Shahabaz-Bagwan/ultra-choc-wings/case/ultra_choc_wings_case.scad

// Ultra Choc Wings uniboard case. Generated by scripts/make_case.py from the PCB;
// edit the parameters below, not the data.
//
// One piece holds both halves (left PCB switch side up, right PCB flipped)
// at a fixed splay. Each half drops into its pocket and sits flat on the
// floor (every SMD part is on the top side, so the bottom is bare), held by
// three M2 screws that self-tap into the floor. The CR2032 is reachable from
// the top; the top-edge notch clears the XIAO USB-C and the power switch.

/* [Layout] */
splay = 12;        // degrees each half is rotated away from straight
gap = 18;          // mm between the two halves at their closest point
/* [Walls] */
wall = 2.4;        // side wall thickness
floor_t = 3;       // floor under the PCB
clearance = 0.4;   // gap between PCB edge and pocket wall
pcb_t = 1.6;
lip = 1.0;         // wall height above the PCB top surface
/* [Screws] */
pilot_d = 1.7;     // M2 self-tapping pilot (use 3.2 for M2 heat-set inserts)
pilot_depth = 2.6;
/* [Details] */
xiao_relief_depth = 2;
notch_depth = 10;  // how far the top-edge notch reaches into the wall
center_tray = true; // hollow the deck between the halves
$fn = 48;

board = [[35.195, 62.881], [35.383, 62.824], [35.556, 62.731], [35.707, 62.607], [35.831, 62.456], [35.924, 62.283], [35.981, 62.095], [36.0, 61.9], [36.0, 61.5], [36.019, 61.305], [36.076, 61.117], [36.169, 60.944], [36.293, 60.793], [36.444, 60.669], [36.617, 60.576], [36.805, 60.519], [37.0, 60.5], [44.5, 60.5], [44.695, 60.481], [44.883, 60.424], [45.056, 60.331], [45.207, 60.207], [45.331, 60.056], [45.424, 59.883], [45.481, 59.695], [45.5, 59.5], [45.5, 54.875], [45.519, 54.68], [45.576, 54.492], [45.669, 54.319], [45.793, 54.168], [45.944, 54.044], [46.117, 53.951], [46.305, 53.894], [46.5, 53.875], [62.5, 53.875], [62.695, 53.856], [62.883, 53.799], [63.056, 53.706], [63.207, 53.582], [63.331, 53.431], [63.424, 53.258], [63.481, 53.07], [63.5, 52.875], [63.5, 52.5], [63.519, 52.305], [63.576, 52.117], [63.669, 51.944], [63.793, 51.793], [63.944, 51.669], [64.117, 51.576], [64.305, 51.519], [64.5, 51.5], [80.5, 51.5], [80.695, 51.481], [80.883, 51.424], [81.056, 51.331], [81.207, 51.207], [81.331, 51.056], [81.424, 50.883], [81.481, 50.695], [81.5, 50.5], [81.5, 0.5], [81.273, 0.5], [81.08, 0.481], [80.895, 0.426], [80.724, 0.336], [80.574, 0.215], [80.449, 0.068], [80.356, -0.101], [80.296, -0.285], [80.273, -0.477], [80.287, -0.67], [80.338, -0.856], [80.424, -1.029], [82.174, -3.838], [82.301, -4.0], [82.457, -4.134], [82.638, -4.232], [82.835, -4.291], [83.04, -4.309], [83.244, -4.284], [83.439, -4.218], [83.616, -4.114], [83.769, -3.976], [83.889, -3.809], [84.273, -3.145], [84.387, -2.985], [84.53, -2.851], [84.697, -2.748], [84.88, -2.679], [85.073, -2.647], [85.269, -2.653], [85.46, -2.698], [85.639, -2.779], [100.361, -11.279], [100.521, -11.393], [100.655, -11.536], [100.758, -11.703], [100.827, -11.886], [100.859, -12.079], [100.853, -12.275], [100.808, -12.466], [100.727, -12.645], [93.227, -25.635], [93.113, -25.795], [92.97, -25.929], [92.803, -26.032], [92.62, -26.101], [92.427, -26.133], [92.231, -26.127], [92.04, -26.082], [91.861, -26.001], [79.743, -19.005], [79.57, -18.926], [79.384, -18.881], [79.194, -18.872], [79.005, -18.9], [78.825, -18.963], [75.488, -20.5], [75.385, -20.883], [75.316, -21.067], [75.213, -21.233], [75.079, -21.376], [74.919, -21.49], [74.741, -21.571], [74.55, -21.616], [74.354, -21.622], [74.16, -21.59], [73.852, -21.508], [73.624, -21.474], [73.394, -21.494], [73.175, -21.565], [64.569, -25.53], [64.367, -25.598], [64.155, -25.622], [63.944, -25.601], [33.851, -19.252], [33.641, -19.23], [33.431, -19.253], [33.231, -19.32], [33.049, -19.427], [32.893, -19.57], [32.372, -20.133], [31.822, -20.667], [31.244, -21.171], [30.641, -21.644], [30.013, -22.085], [29.363, -22.492], [28.692, -22.863], [28.003, -23.199], [27.296, -23.498], [26.575, -23.759], [25.841, -23.982], [25.097, -24.165], [24.344, -24.309], [23.584, -24.413], [22.819, -24.477], [22.053, -24.5], [21.286, -24.482], [20.522, -24.424], [19.761, -24.326], [19.007, -24.188], [18.261, -24.01], [17.525, -23.792], [16.802, -23.536], [16.094, -23.243], [15.402, -22.912], [14.729, -22.545], [14.076, -22.143], [13.445, -21.707], [12.838, -21.238], [12.256, -20.738], [11.702, -20.208], [11.177, -19.649], [10.682, -19.064], [10.218, -18.453], [9.788, -17.818], [9.392, -17.161], [9.031, -16.485], [8.706, -15.79], [8.419, -15.079], [8.169, -14.354], [8.085, -14.16], [7.962, -13.989], [7.805, -13.847], [7.623, -13.741], [7.422, -13.676], [-7.933, -10.436], [-8.128, -10.373], [-8.307, -10.272], [-8.46, -10.137], [-8.583, -9.973], [-8.671, -9.788], [-8.718, -9.589], [-8.724, -9.384], [-8.688, -9.182], [-8.612, -8.992], [-8.499, -8.822], [-8.353, -8.678], [-8.131, -8.5], [-8.5, -8.5], [-8.695, -8.481], [-8.883, -8.424], [-9.056, -8.331], [-9.207, -8.207], [-9.331, -8.056], [-9.424, -7.883], [-9.481, -7.695], [-9.5, -7.5], [-9.5, 61.9], [-9.481, 62.095], [-9.424, 62.283], [-9.331, 62.456], [-9.207, 62.607], [-9.056, 62.731], [-8.883, 62.824], [-8.695, 62.881], [-8.5, 62.9], [35.0, 62.9]];
holes = [[2.0, -10.8], [24.5, 59.5], [76.5, -2.5]];
xiao_relief = [-9.14, 42.75, 8.95, 64.41]; // [x0, y0, x1, y1]
notch_x = [-10.14, 22.0];
board_top = 62.9;
coin = [22.0, -10.0];

// Place the left half so its inner edge sits gap/2 left of x = 0.
function rot(p, a) = [p[0] * cos(a) - p[1] * sin(a), p[0] * sin(a) + p[1] * cos(a)];
inner_x = max([for (p = board) rot(p, -splay)[0]]);

module place_left() translate([-gap / 2 - inner_x, 0]) rotate(-splay) children();
module place_right() mirror([1, 0]) place_left() children();
module both() { place_left() children(); place_right() children(); }

h = floor_t + pcb_t + lip;

module board_shape() polygon(board);

module outer_shape() offset(r = wall + clearance) hull() both() board_shape();

module pockets() both() offset(delta = clearance) board_shape();

module case() {
    difference() {
        linear_extrude(h) outer_shape();
        // PCB pockets
        translate([0, 0, floor_t]) linear_extrude(h) pockets();
        // Deck between the halves
        if (center_tray)
            translate([0, 0, floor_t]) linear_extrude(h)
                // offset in, then out: drops slivers too thin to be useful
                offset(r = 3) offset(delta = -3) difference() {
                    offset(r = -wall) outer_shape();
                    offset(r = wall + clearance) both() board_shape();
                }
        // XIAO pin relief
        translate([0, 0, floor_t - xiao_relief_depth]) linear_extrude(h)
            both() offset(delta = 1)
                translate([xiao_relief[0], xiao_relief[1]])
                    square([xiao_relief[2] - xiao_relief[0], xiao_relief[3] - xiao_relief[1]]);
        // USB-C / power switch notch in the top wall
        translate([0, 0, floor_t]) linear_extrude(h)
            both() translate([notch_x[0], board_top - 1])
                square([notch_x[1] - notch_x[0], notch_depth]);
        // M2 pilot holes
        both() for (p = holes) translate([p[0], p[1], floor_t - pilot_depth])
            linear_extrude(pilot_depth + 0.01) circle(d = pilot_d);
    }
}

case();
