Shahabaz-Bagwan/ultra-choc-wings/output/outlines/top_plate.yaml

models:
    export:
        models:
            a:
                models:
                    a:
                        models:
                            a:
                                models:
                                    a:
                                        models:
                                            a:
                                                models:
                                                    a:
                                                        models:
                                                            a:
                                                                models:
                                                                    a:
                                                                        models:
                                                                            a:
                                                                                models:
                                                                                    a:
                                                                                        models:
                                                                                            a:
                                                                                                models:
                                                                                                    a:
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
                                                                                origin:
                                                                                    - 47
                                                                                    - 21.375
                                                                                end:
                                                                                    - 61
                                                                                    - 21.375
                                                                            ShapeLine2:
                                                                                type: line
                                                                                origin:
                                                                                    - 61
                                                                                    - 21.375
                                                                                end:
                                                                                    - 61
                                                                                    - 35.375
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
