Shahabaz-Bagwan/ultra-choc-wings/output/outlines/board.yaml

models:
    export:
        models:
            a:
                models: {}
                origin:
                    - 0
                    - 0
            b:
                models:
                    a:
                        models: {}
                        origin:
                            - 0
                            - 0
                    b:
                        paths:
                            p1:
                                type: line
                                origin:
                                    - -9.5
                                    - -8.212090332786886
                                end:
                                    - -9.5
                                    - 59.9
                            p2:
                                type: line
                                origin:
                                    - -6.5
                                    - 62.9
                                end:
                                    - 39.62981965576927
                                    - 62.9
                            p3:
                                type: line
                                origin:
                                    - 40.35907642628079
                                    - 62.810014582329636
                                end:
                                    - 79.22925677051151
                                    - 53.06905372498025
                            p4:
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
                        type: arc
                    fillet7:
                        origin:
                            - -6.5
                            - -8.212090332786886
                        radius: 3
                        startAngle: 180
                        endAngle: 241.58733657420757
                        type: arc
                origin:
                    - 0
                    - 0
        origin:
            - 0
            - 0
units: mm
origin:
    - 0
    - 0
